7eraflops/prj23/firmware/components/board_manager/include/board_manager.hpp

#pragma once

#include <driver/gpio.h>

#include <esp_err.h>
#include <functional>

namespace board_manager {

/**
 * @brief Initialize the internal MCU temperature sensor.
 */
void init_temperature_sensor();

/**
 * @brief Get the current MCU temperature in Celsius.
 *
 * @return float Temperature in Celsius, or 0.0f if the sensor is not initialized.
 */
float get_mcu_temperature();

/**
 * @brief Initialize the board manager and start monitoring the specified GPIO for a long press.
 */
esp_err_t init_reset_button(gpio_num_t gpio_num, uint32_t hold_time_ms,
                            std::function<void()> on_long_press);

} // namespace board_manager
